ccadic/RackDoubleNerdminer/pictures/20230723_130305.jpg

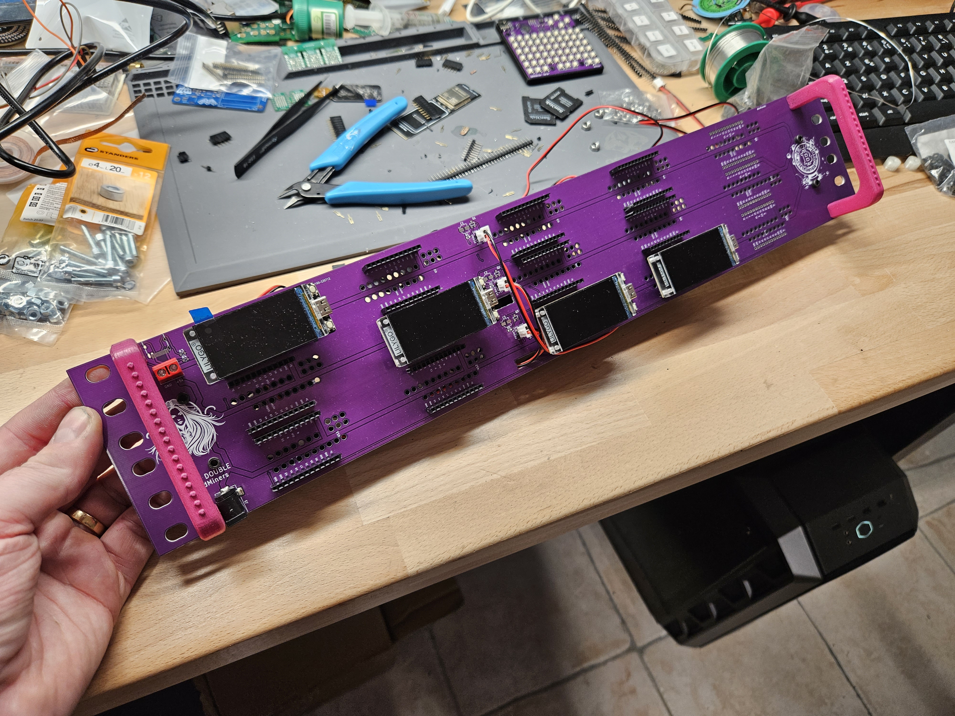
pictures/20230723_130305.jpg
