ccadic/RackDoubleNerdminer/pictures/20230723_130313.jpg

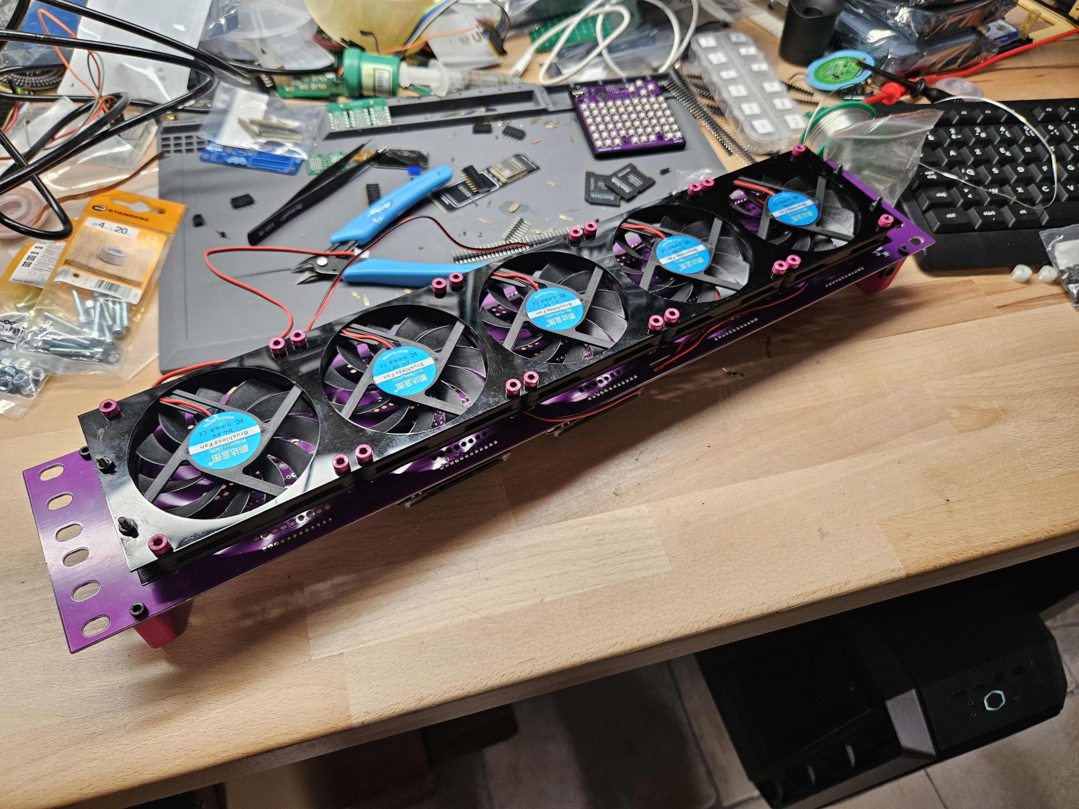
pictures/20230723_130313.jpg
