ccadic/RackDoubleNerdminer/pictures/20230723_130330.jpg

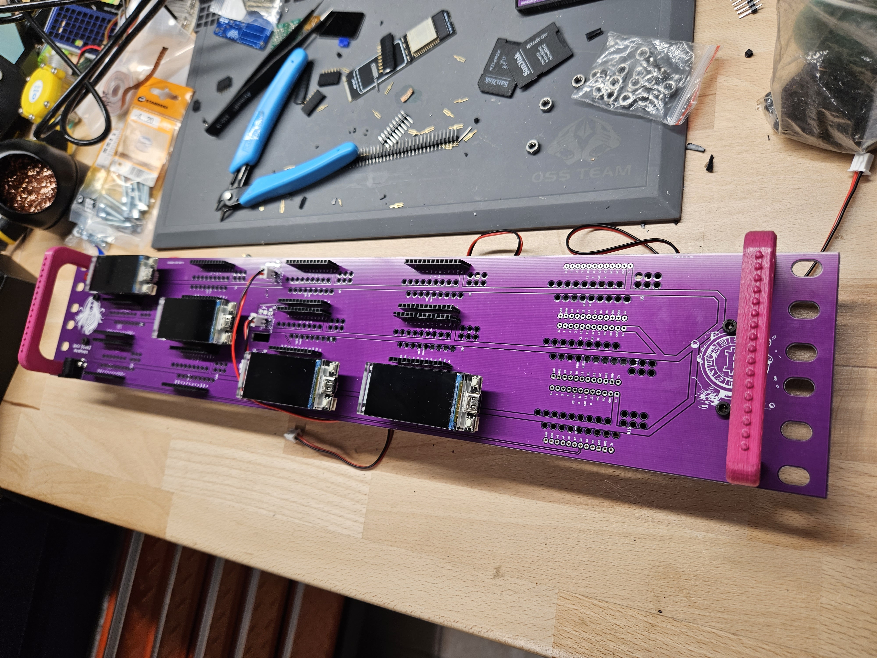
pictures/20230723_130330.jpg
