ccadic/RackDoubleNerdminer/pictures/20230723_130340.jpg

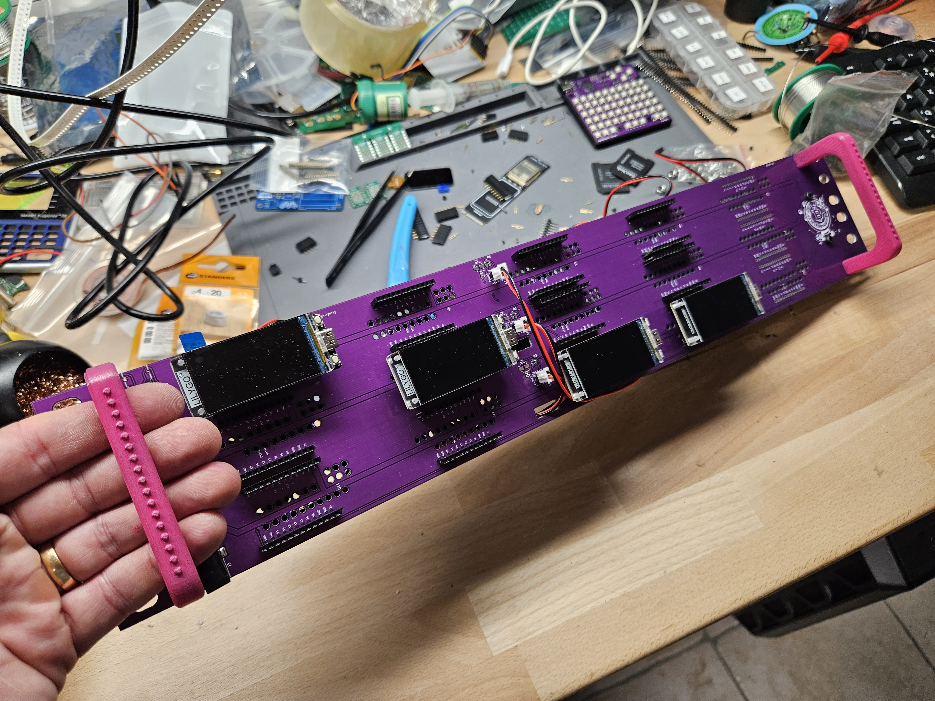
pictures/20230723_130340.jpg
