ccadic/RackDoubleNerdminer/pictures/doubleracksolid.JPG

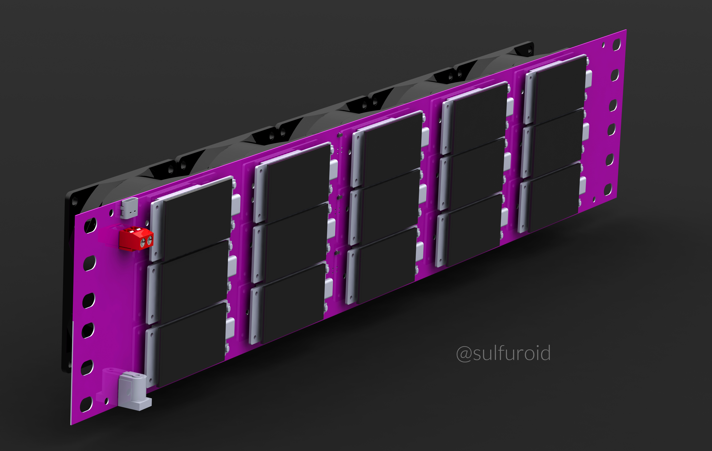
pictures/doubleracksolid.JPG
